daveatpanic/PlaydateCabinet/mirrorpi/controls.h

//
//  controls.h
//  MirrorJr
//
//  Created by Dave Hayden on 9/28/24.
//

#ifndef controls_h
#define controls_h

#include <stdbool.h>

bool controls_init();
void controls_scan();

#endif /* controls_h */
